vives-project-xp/Snot/box/src/board/buzzer/Buzzer.h

#pragma once

#include "mbed.h"

class Buzzer{
    private:
        PwmOut pwm;

    public:
        Buzzer();
        void playFreq(float frequency, float duration, float volume);
        void buttonBeep();
        void startupSound();
        void completeSound();
        void failSound();
        void keypadBeep(char button);
};
